lambdawolflabs/555-Timer-Functional-Complete-Logic-Gates/Photos/Board_Idle_Current_20220109_141949.jpg

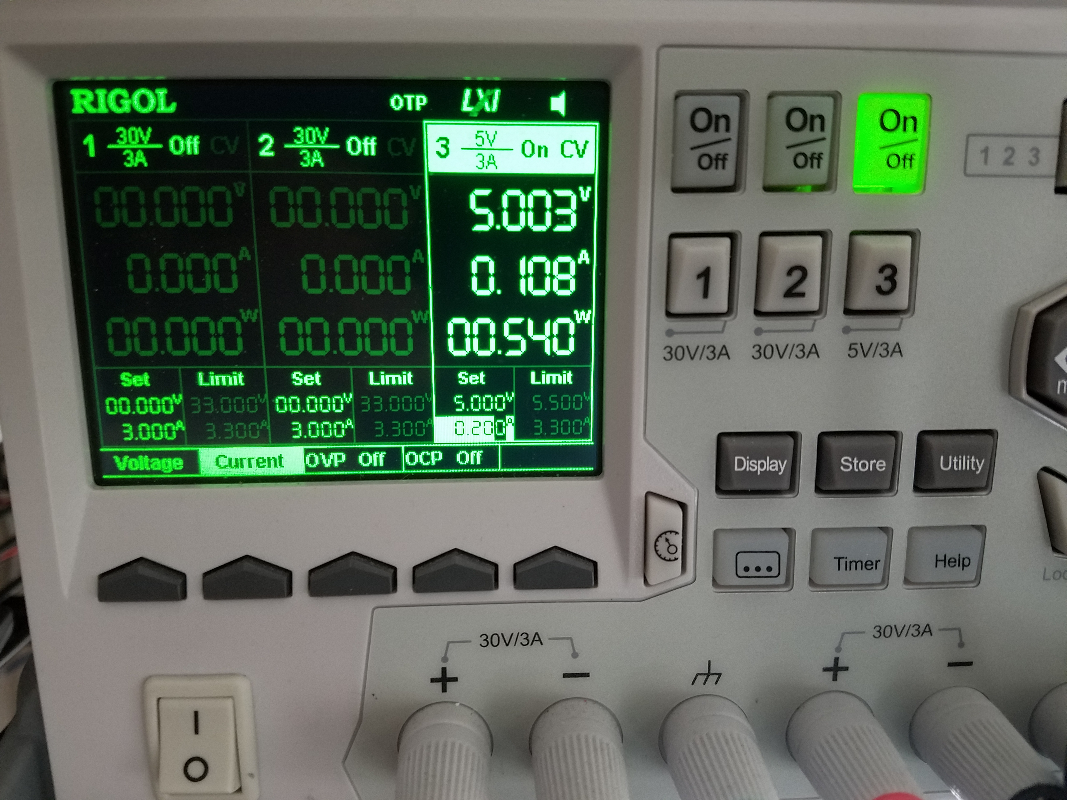
Photos/Board_Idle_Current_20220109_141949.jpg
