lambdawolflabs/555-Timer-Functional-Complete-Logic-Gates/Photos/PSU_and_SigGen_Used_20220109_152748.jpg

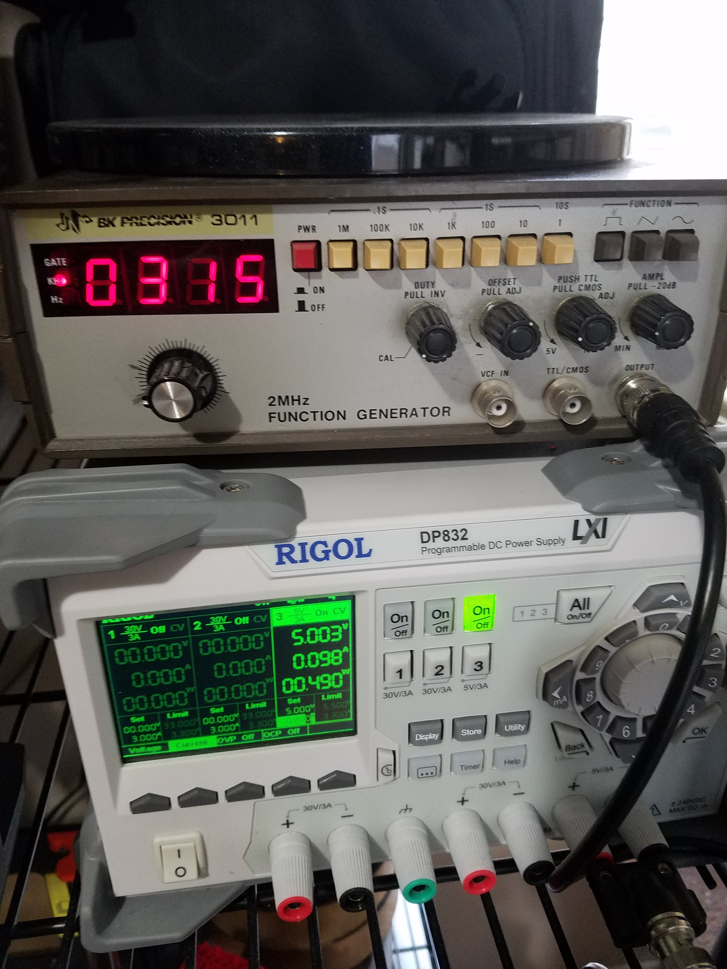
Photos/PSU_and_SigGen_Used_20220109_152748.jpg
