lambdawolflabs/555-Timer-Functional-Complete-Logic-Gates/Photos/ScopeChASettings_20220109_153158.jpg

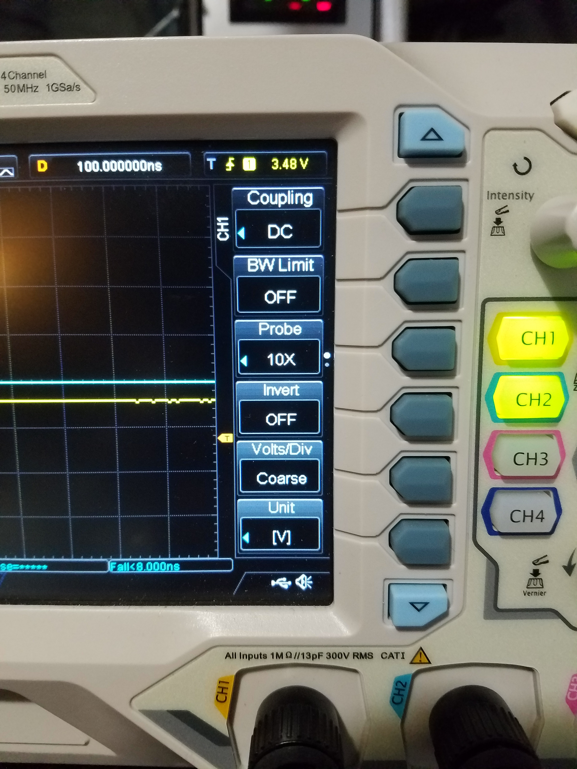
Photos/ScopeChASettings_20220109_153158.jpg
