lambdawolflabs/555-Timer-Functional-Complete-Logic-Gates/Propagation Times Scope Shots/ANDF.png

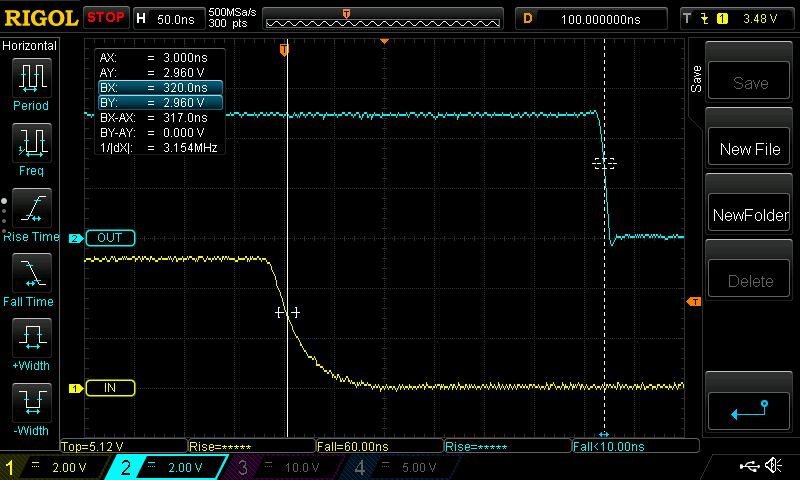
Propagation Times Scope Shots/ANDF.png
