lambdawolflabs/555-Timer-Functional-Complete-Logic-Gates/Propagation Times Scope Shots/ANDR.png

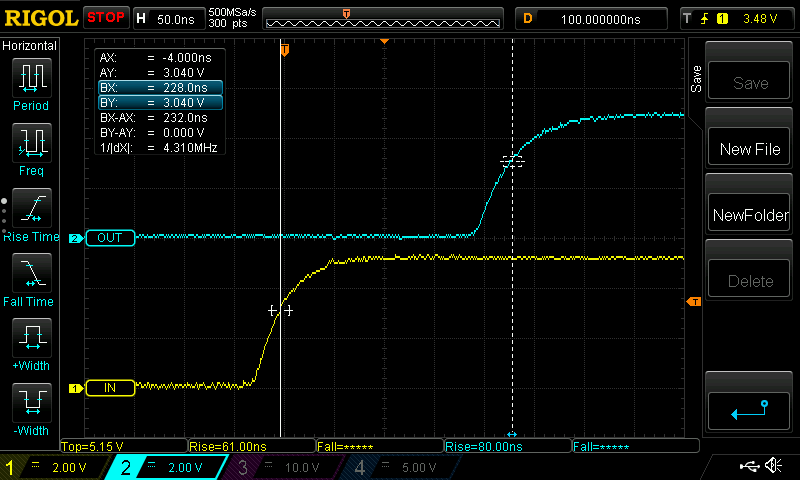
Propagation Times Scope Shots/ANDR.png
