lambdawolflabs/555-Timer-Functional-Complete-Logic-Gates/Propagation Times Scope Shots/DFFF.png

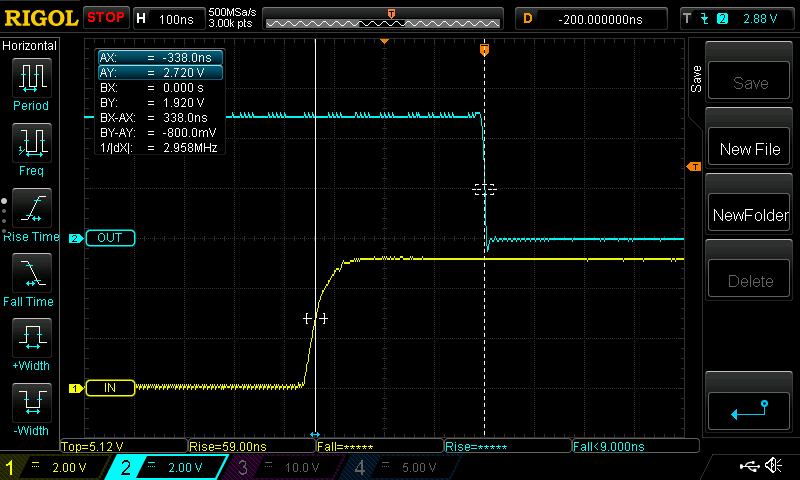
Propagation Times Scope Shots/DFFF.png
