lambdawolflabs/555-Timer-Functional-Complete-Logic-Gates/Propagation Times Scope Shots/DFFR.png

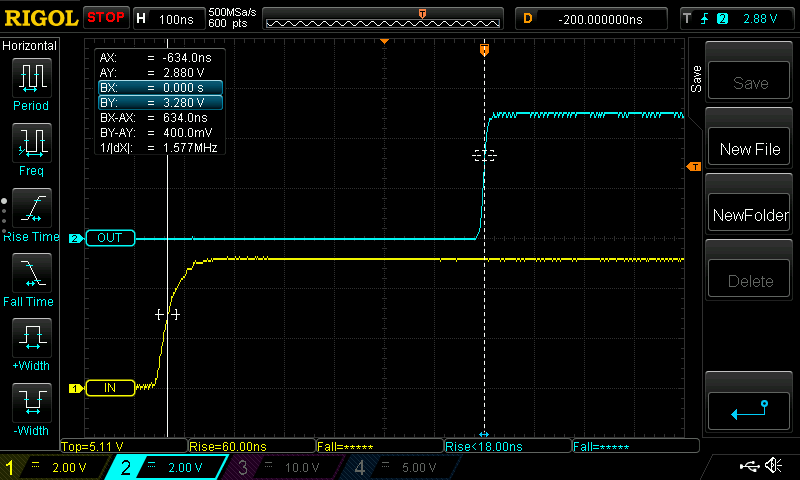
Propagation Times Scope Shots/DFFR.png
