lambdawolflabs/555-Timer-Functional-Complete-Logic-Gates/Propagation Times Scope Shots/NORF.png

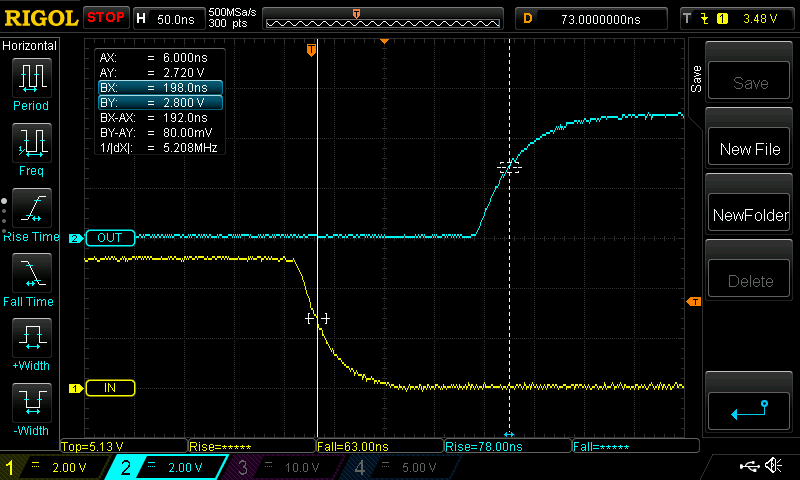
Propagation Times Scope Shots/NORF.png
