lambdawolflabs/555-Timer-Functional-Complete-Logic-Gates/Propagation Times Scope Shots/NOTF.png

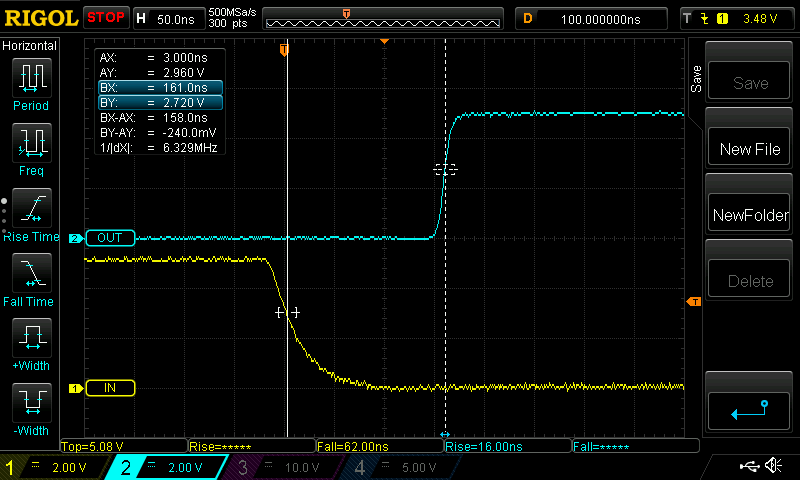
Propagation Times Scope Shots/NOTF.png
