lambdawolflabs/555-Timer-Functional-Complete-Logic-Gates/Propagation Times Scope Shots/NOTR.png

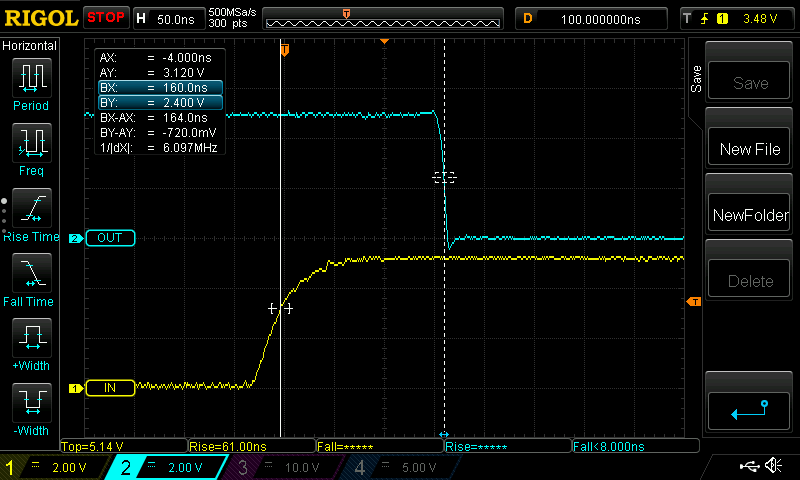
Propagation Times Scope Shots/NOTR.png
