lambdawolflabs/555-Timer-Functional-Complete-Logic-Gates/Propagation Times Scope Shots/XORF.png

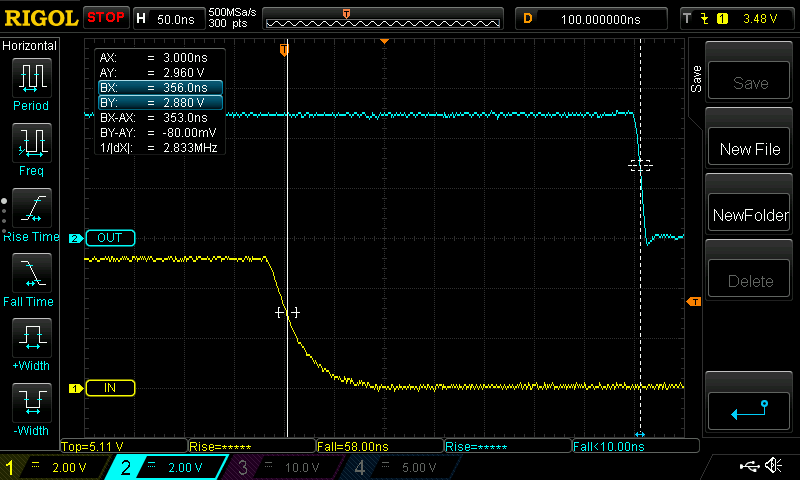
Propagation Times Scope Shots/XORF.png
