lambdawolflabs/555-Timer-Functional-Complete-Logic-Gates/Propagation Times Scope Shots/XORR.png

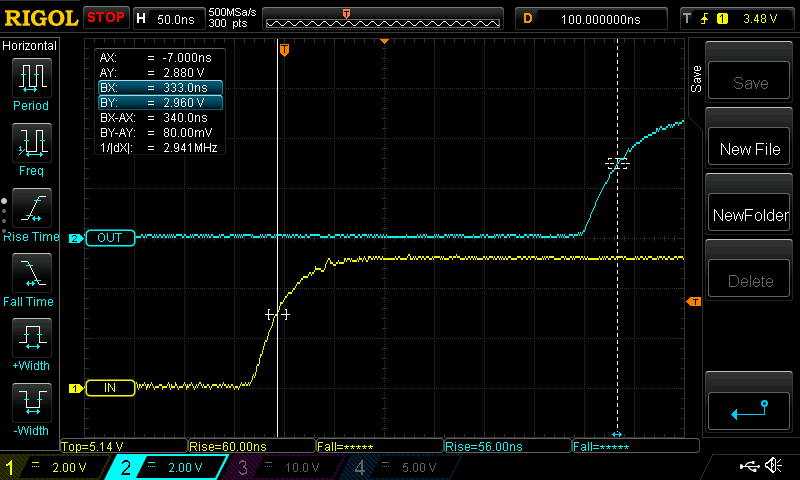
Propagation Times Scope Shots/XORR.png
