lambdawolflabs/555-Timer-Functional-Complete-Logic-Gates/Simulations/AdderOut.png

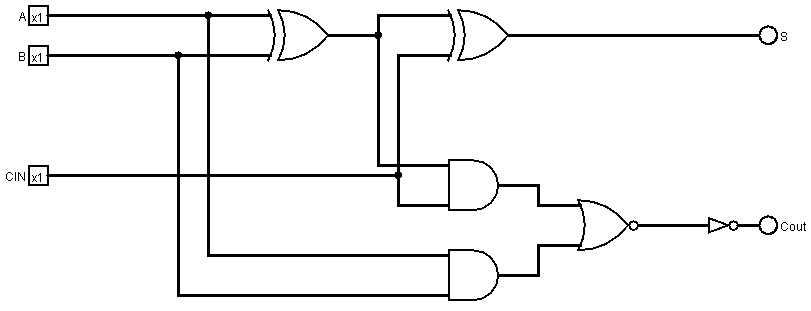
Simulations/AdderOut.png
