lambdawolflabs/555-Timer-Functional-Complete-Logic-Gates/Photos/Assembled_Board_Overview_Bottom_20220109_170110.jpg

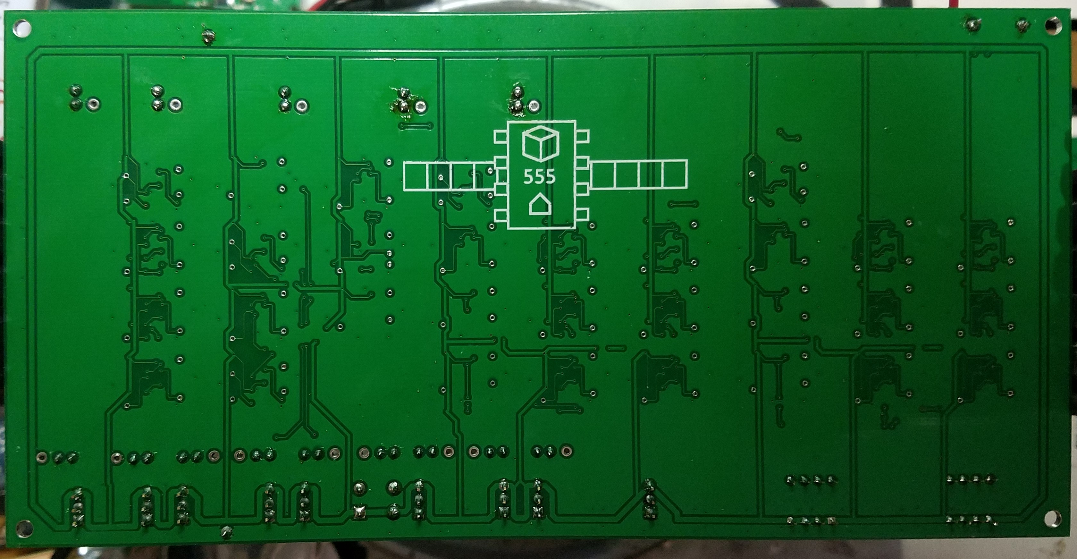
Photos/Assembled_Board_Overview_Bottom_20220109_170110.jpg
