lambdawolflabs/555-Timer-Functional-Complete-Logic-Gates/Photos/BreadboardTests_20211204_153255.jpg

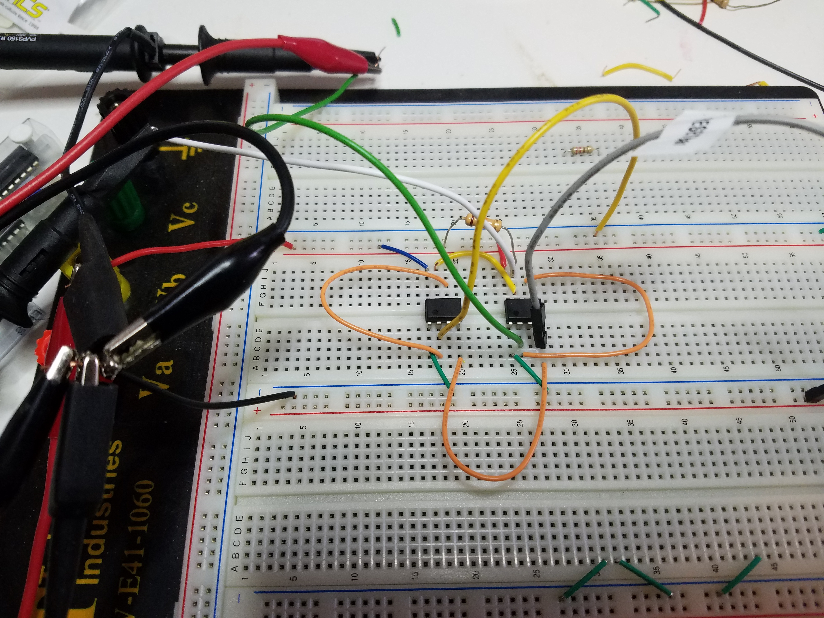
Photos/BreadboardTests_20211204_153255.jpg
