lambdawolflabs/555-Timer-Functional-Complete-Logic-Gates/Simulations/555_AND_Gate.asc

R1: res; 10k
U1: NE555
U2: NE555
V1: voltage; 5
V2: voltage; PULSE(0 5 0.25 1N 1N 1 2 2)
V3: voltage; PULSE(0 5 1 1N 1N 0.5 2 2)
Named nets: 0, VCC, INPUT_A, INPUT_B, AND_OUTPUT
AND Gate
.tran 0 2 0 1
