lambdawolflabs/555-Timer-Functional-Complete-Logic-Gates/Simulations/555_D_Flip_Flop.asc

R2: res; 10k
R3: res; 10k
U1: NE555
U2: NE555
U3: NE555
U4: NE555
U5: NE555
U6: NE555
U7: NE555
U8: NE555
U9: NE555
V1: voltage; 5
V2: voltage; PULSE(0 5 0.25 1N 1N 0.5 1)
V3: voltage; PULSE(0 5 0.1 1N 1N 0.125 0.25)
Named nets: 0, VCC, DATA_INV, CLOCK_INV, INPUT_DATA, INPUT_CLOCK, NOR_OUTPUT_2, AND_OUT, NOR_OUTPUT2_INV, DATA_INV_2, DFF_Q_OUT
INV
.tran 0 2 0 1
NOR GATE
AND
NOR Gate w/ Inverter Outputs
INV
