lambdawolflabs/555-Timer-Functional-Complete-Logic-Gates/Simulations/555_XOR_Gate.asc

R1: res; 10k
R2: res; 10k
R3: res; 10k
U1: NE555
U2: NE555
U3: NE555
U4: NE555
U5: NE555
U6: NE555
V1: voltage; 5
V2: voltage; PULSE(0 5 0.25 1N 1N 1 2 2)
V3: voltage; PULSE(0 5 1 1N 1N 0.5 2 2)
Named nets: 0, VCC, INPUT_A_INV, INPUT_B_INV, INPUT_A, INPUT_B, NOR_OUTPUT_1, NOR_OUTPUT_2, XOR_OUTPUT
NOR Gate w/ Inverter Outputs
.tran 0 2 0 1
NOR Gate w/ Inverter Outputs
NOR Gate w/ Inverter Outputs
