lambdawolflabs/555-Timer-Functional-Complete-Logic-Gates/Photos/PasteApplied_20220108_132210.jpg

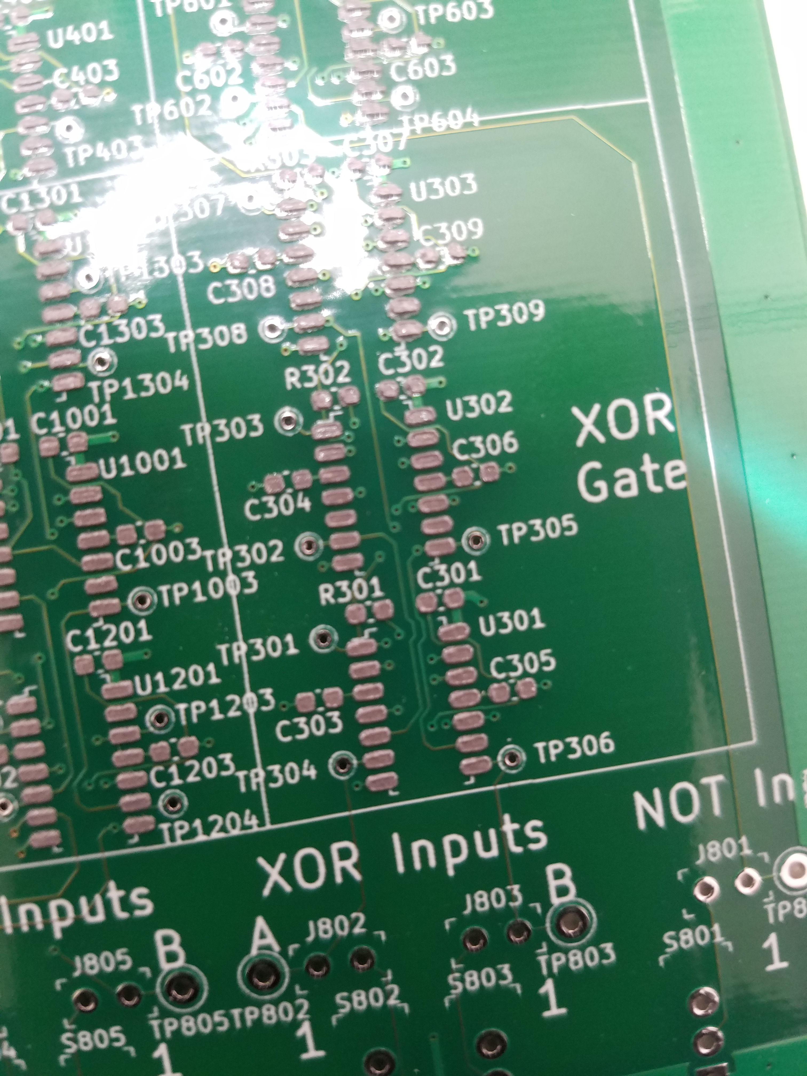
Photos/PasteApplied_20220108_132210.jpg
