lambdawolflabs/555-Timer-Functional-Complete-Logic-Gates/Photos/DFF_PropTest_Setup_20220109_155415.jpg

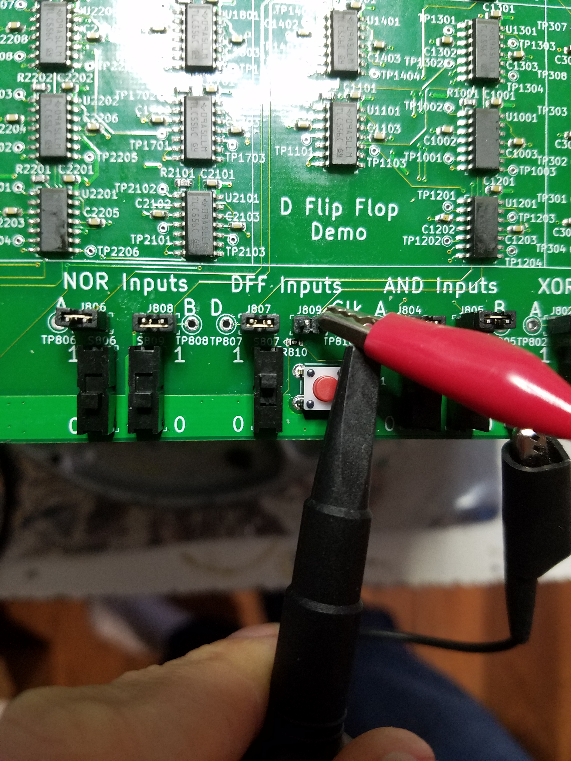
Photos/DFF_PropTest_Setup_20220109_155415.jpg
