lambdawolflabs/555-Timer-Functional-Complete-Logic-Gates/Photos/GatePropagationTestSetup_20220109_152803.jpg

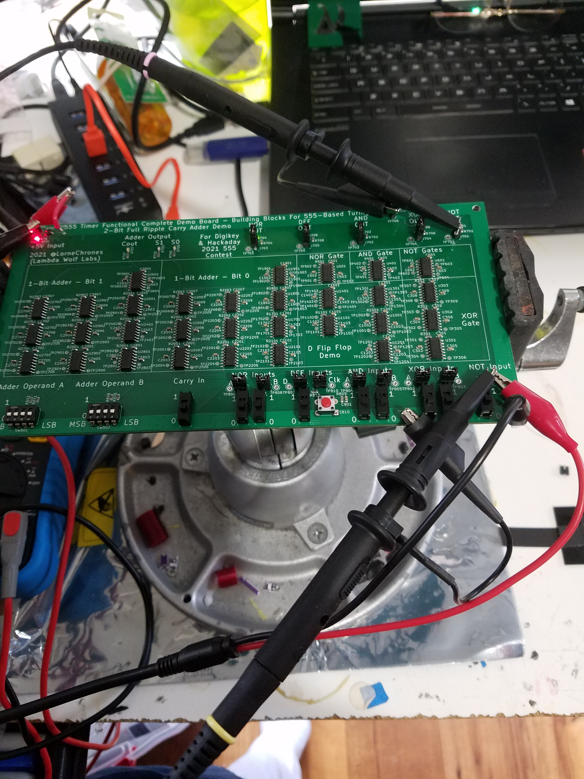
Photos/GatePropagationTestSetup_20220109_152803.jpg
